Aidan-McNay/chimes-leds/sensors/light.cpp

// =======================================================================
// imu.cpp
// =======================================================================
// Definitions of the IMU functions

#include "sensors/light.h"
#include "hardware/i2c.h"
#include "utils/fix15.h"
#include <cstdio>

// ----------------------------------------------------------------------
// I2C Helper functions
// ----------------------------------------------------------------------

void LightSensor::write( uint8_t addr, uint16_t data )
{
  uint8_t buf[] = { addr, (uint8_t) (data >> 8), (uint8_t) (data & 0xFF) };
  i2c_write_blocking( I2C_CHAN, ADDRESS, buf, 3, false );
}

uint16_t LightSensor::read( uint8_t addr )
{
  printf("Reading address %d\n", addr);
  i2c_write_blocking( I2C_CHAN, ADDRESS, &addr, 1, true );
  static uint8_t buf[2];
  i2c_read_blocking( I2C_CHAN, ADDRESS, buf, 2, false );

  printf("Read data %d %d\n", buf[0], buf[1]);

  return ( buf[0] << 8 ) | buf[1];
}

// ----------------------------------------------------------------------
// Constructor
// ----------------------------------------------------------------------

LightSensor::LightSensor( int gpio_sda, int gpio_scl )
  :gpio_sda(gpio_sda), gpio_scl(gpio_scl) {}

// ----------------------------------------------------------------------
// Init
// ----------------------------------------------------------------------
void LightSensor::init() {
  // Initialize I2C Channel
  i2c_init( I2C_CHAN, I2C_BAUD_RATE );

  // Configure GPIOs for I2C
  gpio_set_function( gpio_sda, GPIO_FUNC_I2C );
  gpio_set_function( gpio_scl, GPIO_FUNC_I2C );

  configure( MS_800, TIMES_2 );
  set_power_mode( LEAST );
}

// ----------------------------------------------------------------------
// Configure light sensor gain and integration time
// ----------------------------------------------------------------------

void LightSensor::configure( integration_time_t it, gain_t g )
{
  // Bits 12:11 are reserved for the gain
  // Bits 9:6 are reserved for the integration time
  // All other bits can be 0
  uint16_t config = ( g << 11 ) | ( it << 6 );

  write( ALS_CONF, config );
}

void LightSensor::set_power_mode( power_save_mode_t mode )
{
  // Bits 2:0 are reserved for the power save mode
  // All other bits must be 0
  uint16_t config = mode;

  write( Power_saving, config );
}

// -------------------------------------------------------------------------
// LightSensor::resolution
// -------------------------------------------------------------------------

fix15 LightSensor::resolution()
{
  // Table of resolution values based off of gain and integration time are defined here:
  // https://www.vishay.com/docs/84367/designingveml6030.pdf

  // Simple calculation shows that resolution can be calculated via
  // Resolution = 6.72 / ( gain * integration_time )

  return divfix15( float2fix15(6.72), 
                 multfix15( int2fix15( gain ), int2fix15( integration_time ) ) );
}

fix15 LightSensor::sample()
{
  uint16_t data = read( ALS );

  printf("Light data: %d\n", data);

  // Use the formula that Lux = data * resolution
  return multfix15( resolution(), int2fix15( data ) );
}
