Aidan-McNay/chimes-leds/interface/pico_led.cpp

#include "pico/stdlib.h"
#ifdef CYW43_WL_GPIO_LED_PIN
#include "pico/cyw43_arch.h"
#endif


// Perform initialisation
int pico_led_init( void )
{
#if defined( PICO_DEFAULT_LED_PIN )
  // A device like Pico that uses a GPIO for the LED will define
  // PICO_DEFAULT_LED_PIN so we can use normal GPIO functionality to turn
  // the led on and off
  gpio_init( PICO_DEFAULT_LED_PIN );
  gpio_set_dir( PICO_DEFAULT_LED_PIN, GPIO_OUT );
  return PICO_OK;
#elif defined( CYW43_WL_GPIO_LED_PIN )
  // For Pico W devices we need to initialise the driver etc
  return cyw43_arch_init();
#endif
}

// Turn the led on or off
void pico_set_led( bool led_on )
{
#if defined( PICO_DEFAULT_LED_PIN )
  // Just set the GPIO on or off
  gpio_put( PICO_DEFAULT_LED_PIN, led_on );
#elif defined( CYW43_WL_GPIO_LED_PIN )
  // Ask the wifi "driver" to set the GPIO on or off
  cyw43_arch_gpio_put( CYW43_WL_GPIO_LED_PIN, led_on );
#endif
}
